Dominik-Workshop/Linear_power_supply/simulations/v2-fix_oscilations/new_bode.asc

C1: cap; 10µ
C2: cap; 1n
C3: cap; 100n
C4: cap; 100n
D1: schottky; 1N5819
I_set: voltage; 1
Q1: npn; BC846B
Q2: npn; 2N3055
Q3: npn; 2N3055
Q4: npn; 2N3055
Q5: npn; 2N3055
Q6: pnp; 2SA2094
R1: res; 47k
R2: res; 10k
R3: res; 100
R4: res; 1k
R5: res; 1k
R6: res; 1k
R7: res; 6.8
R8: res; 5k6
R9: res; 0.1
R10: res; 0.1
R11: res; 0.1
R12: res; 0.1
R13: res; 0.05
R14: res; 1
U1: lm358
U2: lm358
V1: voltage; 15
V2: voltage; 30
V3: voltage; 0.1; AC 0.1
V_set: voltage; 3
Named nets: 0, +15V, VIN, v_out+, v_out-, v_+
.ac dec 100 10 10000000
(V(v_out+)-V(v_out-))/(V(v_out+)-V(v_+))
